kitfitz/flicker-candle/pics/flicker-candle.jpeg

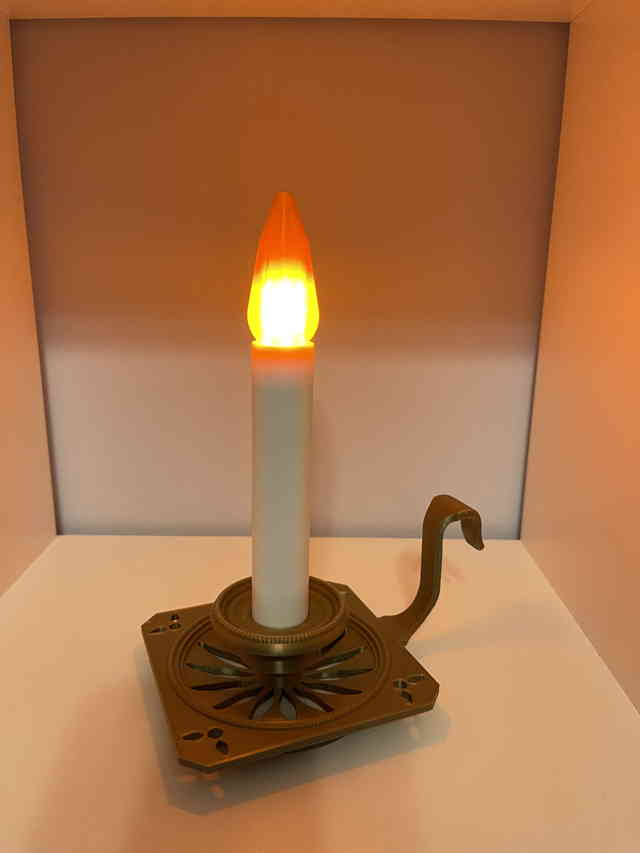
pics/flicker-candle.jpeg
