kitfitz/flicker-candle/electrical/flicker-charger/flicker-charger.kicad_sch

## KiCad design electrical/flicker-charger/flicker-charger.kicad_sch (2025-12-21)

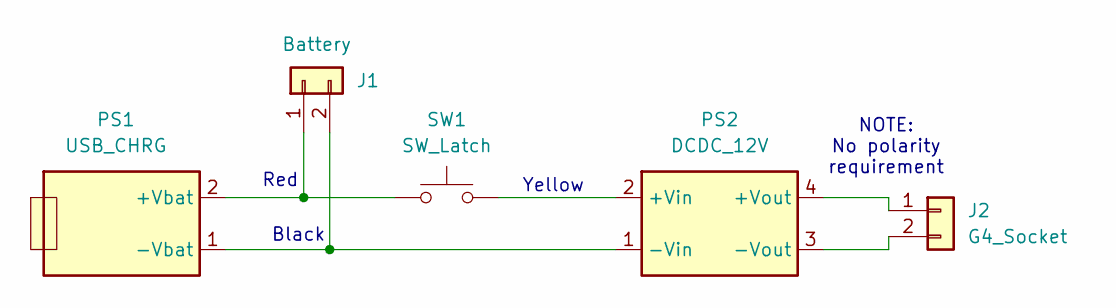
[picture p36: schematic flicker-charger.kicad_sch]

Parts:
J1: Battery
J2: G4_Socket
PS1: USB_CHRG
PS2: DCDC_12V
SW1: SW_Latch

Connections:
unnamed: J1.1, PS1.2 (+Vbat), SW1.1
unnamed: J1.2, PS1.1 (-Vbat), PS2.1 (-Vin)
unnamed: J2.1, PS2.4 (+Vout)
unnamed: J2.2, PS2.3 (-Vout)
unnamed: PS2.2 (+Vin), SW1.2

Notes on the sheet:
Yellow
Red
NOTE: No polarity requirement
Black
